jaisor/wifi-climate-sensor/assets/schematic_eagle.sch

## EAGLE design assets/schematic_eagle.sch (2025-02-25)

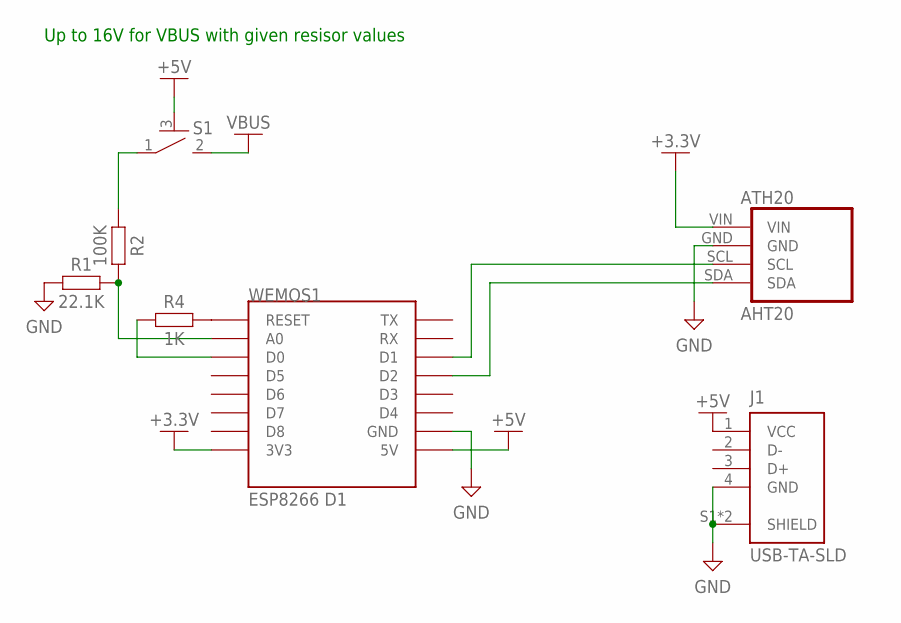
[picture p8: schematic schematic_eagle.sch]

Parts:
ATH20: AHT20
J1: USB-TA-SLD
R1: 22.1K; RESC2012X65
R2: 100K; RESC2012X65
R4: 1K; RESC2012X65
S1: SMD_SWB3U-1100P(M)1100P(M); SMD_SW
WEMOS1: U1; WEMOS-D1-MINI

Connections:
+3.3V: ATH20.VIN, WEMOS1.3V3
+5V: J1.1 (VCC), S1.3, WEMOS1.5V
GND: ATH20.GND, J1.4 (GND), J1.S1 (SHIELD), R1.1, WEMOS1.GND
unnamed: ATH20.SCL, WEMOS1.D1
unnamed: ATH20.SDA, WEMOS1.D2
unnamed: R4.2, WEMOS1.RESET
unnamed: R4.1, WEMOS1.D0
unnamed: R1.2, R2.2, WEMOS1.A0
unnamed: R2.1, S1.1
VBUS: S1.2

Notes on the sheet:
Up to 16V for VBUS with given resisor values
