jaisor/wifi-climate-sensor/src/Device.cpp

#include <Arduino.h>
#include <functional>
#include <ArduinoLog.h>

#include "Device.h"

#include <Wire.h>

// A device ACKs its address when present, which is enough to tell a BME280 from an AHT20
static bool i2cDevicePresent(uint8_t address) {
  Wire.beginTransmission(address);
  return Wire.endTransmission() == 0;
}

// Repeated-start register read, used to tell the BME280 and BME688 apart: both answer on
// 0x76/0x77, so only the chip id register distinguishes them.
static bool i2cReadRegister(uint8_t address, uint8_t reg, uint8_t *value) {
  Wire.beginTransmission(address);
  Wire.write(reg);
  if (Wire.endTransmission(false) != 0) {
    return false;
  }
  if (Wire.requestFrom(address, (uint8_t)1) != 1) {
    return false;
  }
  *value = Wire.read();
  return true;
}

CDevice::CDevice()
:oneWire(NULL), ds18b20(NULL), bme280(NULL), dht(NULL), aht(NULL), bme688(NULL) {

  tMillisUp = millis();
  tMillisTemp = millis();
  sensorReady = false;

#ifdef OLED
  _display = new Adafruit_SSD1306(OLED_SCREEN_WIDTH, OLED_SCREEN_HEIGHT, &Wire, -1);
  if(!_display->begin(SSD1306_SWITCHCAPVCC, OLED_I2C_ID)) {
      Log.errorln("SSD1306 OLED initialiation failed with ID %x", OLED_I2C_ID);
      while (1);
  }
  _display->clearDisplay();
  _display->setTextColor(WHITE);
#endif

  i2cReady = false;
  tempSensorAddress = 0;
  bme68xVariant = 0;
  bme688ReadingReadyAt = 0;
  gas_resistance = 0;
  tLastIAQPersist = millis();
  lastPersistedBaseline = 0;

  // On some targets the DS18B20 data pin doubles as an I2C line, so leave the bus alone when it is selected
  bool i2cPinConflict = false;
  #if defined(TEMP_SENSOR) && defined(I2C_SDA_PIN) && defined(I2C_SCL_PIN)
    i2cPinConflict = configuration.tempSensor == TEMP_SENSOR_DS18B20
      && (TEMP_SENSOR_PIN == I2C_SDA_PIN || TEMP_SENSOR_PIN == I2C_SCL_PIN);
  #endif

  if (!i2cPinConflict) {
    #if defined(I2C_SDA_PIN) && defined(I2C_SCL_PIN)
      i2cReady = Wire.begin(I2C_SDA_PIN, I2C_SCL_PIN);
      if (!i2cReady) {
        Log.errorln(F("I2C Wire initialization failed on pins SDA:%d, SCL:%d"), I2C_SDA_PIN, I2C_SCL_PIN);
      }
    #else
      Wire.begin();
      i2cReady = true;
    #endif
    delay(1000);
  } else {
    Log.noticeln(F("I2C bus not started, DS18B20 shares a pin with it"));
  }

  tLastReading = 0;

  #if defined(TEMP_SENSOR) && defined(TEMP_SENSOR_AUTODETECT)
  // Adopt whatever climate sensor is actually on the bus when nothing is configured yet,
  // or when the configured I2C sensor does not answer (the board was swapped). An explicit
  // DS18B20/DHT22 choice is left alone, since those are not on I2C at all.
  if (i2cReady) {
    tempSensorType detected = detectI2CTempSensor();
    bool configuredIsI2C = configuration.tempSensor == TEMP_SENSOR_BME280
      || configuration.tempSensor == TEMP_SENSOR_AHT20
      || configuration.tempSensor == TEMP_SENSOR_BME688;

    if (detected != TEMP_SENSOR_UNSUPPORTED
      && detected != configuration.tempSensor
      && (configuration.tempSensor == TEMP_SENSOR_UNSUPPORTED || configuredIsI2C)) {
      Log.noticeln(F("Autodetected climate sensor type %u at I2C 0x%x, replacing configured type %u"),
        detected, tempSensorAddress, configuration.tempSensor);
      configuration.tempSensor = detected;
      EEPROM_saveConfig();
    }
  }
  #endif

  #ifdef TEMP_SENSOR
  switch (configuration.tempSensor) {
    case TEMP_SENSOR_DS18B20: {
      pinMode(TEMP_SENSOR_PIN, INPUT_PULLUP);
      oneWire = new OneWire(TEMP_SENSOR_PIN);
      DeviceAddress da;
      ds18b20 = new DS18B20(oneWire);
      ds18b20->setConfig(DS18B20_CRC);
      ds18b20->begin();

      ds18b20->getAddress(da);
      String addr = "";
      for (uint8_t i = 0; i < 8; i++) {
        if (da[i] < 16) {
          addr += String("o");
        }
        addr += String(da[i], HEX);
      }
      Log.noticeln(F("DS18B20 sensor on pin %d at address: %s"), TEMP_SENSOR_PIN, addr.c_str());
      
      ds18b20->setResolution(12);
      ds18b20->requestTemperatures();

      sensorReady = true;
      tMillisTemp = 0;
    } break;
    
    case TEMP_SENSOR_BME280: {
      if (tempSensorAddress == 0) {
        tempSensorAddress = i2cDevicePresent(BME280_I2C_ID_ALT) ? BME280_I2C_ID_ALT : BME280_I2C_ID;
      }
      bme280 = new Adafruit_BME280();
      if (!bme280->begin(tempSensorAddress)) {
        Log.errorln(F("BME280 sensor initialization failed with ID %x"), tempSensorAddress);
        sensorReady = false;
      } else {
        sensorReady = true;
        tMillisTemp = 0;
      }
      minDelayMs = 100;
      Log.noticeln(F("BME280 Initialized"));
    } break;

    case TEMP_SENSOR_DHT22: {
      dht = new DHT_Unified(TEMP_SENSOR_PIN, DHT22);
      dht->begin();
      sensor_t sensor;
      dht->temperature().getSensor(&sensor);
      Log.noticeln(F("DHT temperature sensor name(%s) v(%u) id(%u) range(%F - %F) res(%F)"),
        sensor.name, sensor.version, sensor.sensor_id, 
        sensor.min_value, sensor.max_value, sensor.resolution);
      dht->humidity().getSensor(&sensor);
      Log.noticeln(F("DHT humidity sensor name(%s) v(%u) id(%u) range(%F - %F) res(%F)"),
        sensor.name, sensor.version, sensor.sensor_id, 
        sensor.min_value, sensor.max_value, sensor.resolution);
      minDelayMs = sensor.min_delay / 1000;
      Log.noticeln(F("DHT sensor min delay %i"), minDelayMs);
    } break;

    case TEMP_SENSOR_AHT20: {
      tempSensorAddress = AHT20_I2C_ID;
      aht = new Adafruit_AHTX0();
      if (!aht->begin()) {
        Log.errorln("Failed to initialize AHT sensor, check wiring");
        sensorReady = false;
      } else {
        sensorReady = true;
        tMillisTemp = 0;
      }
      minDelayMs = 100;
      Log.noticeln(F("AHT20 Initialized"));
    } break;

    case TEMP_SENSOR_BME688: {
      if (tempSensorAddress == 0) {
        tempSensorAddress = i2cDevicePresent(BME280_I2C_ID_ALT) ? BME280_I2C_ID_ALT : BME280_I2C_ID;
      }
      bme688 = new Adafruit_BME680(&Wire);
      if (!bme688->begin(tempSensorAddress, true)) {
        Log.errorln(F("BME688 sensor initialization failed with ID %x"), tempSensorAddress);
        sensorReady = false;
      } else {
        bme688->setTemperatureOversampling(BME680_OS_8X);
        bme688->setHumidityOversampling(BME680_OS_2X);
        bme688->setPressureOversampling(BME680_OS_4X);
        bme688->setIIRFilterSize(BME680_FILTER_SIZE_3);
        bme688->setGasHeater(BME688_GAS_HEATER_TEMP_C, BME688_GAS_HEATER_MS);
        sensorReady = true;
        tMillisTemp = 0;
      }
      // The gas heater makes a reading take a few hundred ms, so it is run asynchronously
      // via beginReading()/endReading() rather than blocking the loop.
      minDelayMs = 100;
      bme688ReadingReadyAt = 0;

      // Continue the baseline saved before the last sleep or restart rather than starting
      // over. Time spent asleep is credited so the day-scale decay tracks wall clock time;
      // the configured interval is the only estimate of it available before NTP is up.
      airQuality.restore(configuration.iaqBaseline, configuration.iaqAccumulatedSec);
      lastPersistedBaseline = configuration.iaqBaseline;
      if (configuration.deepSleepDurationSec > 0 && airQuality.hasBaseline()) {
        airQuality.addElapsedSeconds(configuration.deepSleepDurationSec);
      }

      Log.noticeln(F("%s Initialized"),
        bme68xVariant == BME68X_VARIANT_BME688 ? "BME688" : "BME680");
    } break;

    default:
      sensorReady = false;
      Log.errorln(F("Unsupported temperature sensor: %u"), configuration.tempSensor);
      break;
  }
  #endif

  #ifdef CURRENT_SENSOR
  // Skipped when the bus never came up, so the library cannot quietly re-init it on default pins
  ina219 = i2cReady ? new Adafruit_INA219(INA219_I2C_ID) : NULL;
  currentSensorReady = ina219 != NULL && ina219->begin();
  if (currentSensorReady) {
    Log.noticeln(F("INA219 initialized with ID %x"), INA219_I2C_ID);
  } else {
    Log.warningln(F("INA219 not found with ID %x, current sensing disabled"), INA219_I2C_ID);
    delete ina219;
    ina219 = NULL;
  }
  tMillisCurrent = 0;
  tLastCurrentReading = 0;
  loadVoltage = loadCurrent_mA = loadPower_mW = 0;
  #endif

  #ifdef VOLTAGE_SENSOR
      
  #if defined(CONFIG_IDF_TARGET_ESP32C3)
    pinMode(VOLTAGE_SENSOR_ADC_PIN, ANALOG);
    analogSetPinAttenuation(VOLTAGE_SENSOR_ADC_PIN, ADC_11db);
    analogReadResolution(12);
  #elif defined(SEEED_XIAO_M0)
    pinMode(VOLTAGE_SENSOR_ADC_PIN, ANALOG);
    analogReadResolution(12);
  #elif defined(ESP8266)
    pinMode(VOLTAGE_SENSOR_ADC_PIN, INPUT);
  #endif

  #endif

#if defined(ESP32)
#elif defined(ESP8266)
#elif defined(SEEED_XIAO_M0)
#endif
  
  Log.infoln(F("Device initialized"));
}

#if defined(TEMP_SENSOR) && defined(TEMP_SENSOR_AUTODETECT)
// Probes the addresses the two supported I2C climate sensors use and records which one
// answered, so the BME280 can later be opened on whichever of its two addresses is strapped.
tempSensorType CDevice::detectI2CTempSensor() {
  const uint8_t boschAddresses[] = { BME280_I2C_ID, BME280_I2C_ID_ALT };
  for (uint8_t i = 0; i < sizeof(boschAddresses); i++) {
    uint8_t address = boschAddresses[i];
    uint8_t chipId = 0;
    if (!i2cDevicePresent(address) || !i2cReadRegister(address, BOSCH_REG_CHIP_ID, &chipId)) {
      continue;
    }

    switch (chipId) {
      case BOSCH_CHIP_ID_BME280:
        tempSensorAddress = address;
        Log.noticeln(F("Found BME280 at I2C 0x%x"), address);
        return TEMP_SENSOR_BME280;

      case BOSCH_CHIP_ID_BME68X: {
        tempSensorAddress = address;
        // Same chip id for both; the variant register separates the BME688 from the BME680
        bme68xVariant = 0;
        i2cReadRegister(address, BME68X_REG_VARIANT, &bme68xVariant);
        Log.noticeln(F("Found %s at I2C 0x%x"),
          bme68xVariant == BME68X_VARIANT_BME688 ? "BME688" : "BME680", address);
        return TEMP_SENSOR_BME688;
      }

      default:
        // Most likely a BMP280 (0x58), which has no humidity and is not supported here
        Log.warningln(F("Unrecognized Bosch chip id 0x%x at I2C 0x%x, ignoring"), chipId, address);
        break;
    }
  }

  if (i2cDevicePresent(AHT20_I2C_ID)) {
    tempSensorAddress = AHT20_I2C_ID;
    Log.noticeln(F("Found AHT20 at I2C 0x%x"), tempSensorAddress);
    return TEMP_SENSOR_AHT20;
  }

  Log.noticeln(F("No I2C climate sensor found"));
  return TEMP_SENSOR_UNSUPPORTED;
}
#endif

CDevice::~CDevice() { 
  delete ds18b20;
  delete bme280;
  delete dht;
  delete aht;
  delete bme688;
#ifdef CURRENT_SENSOR
  delete ina219;
#endif
#ifdef OLED
  delete _display;
#endif
  Log.noticeln(F("Device destroyed"));
}

void CDevice::loop() {

  #ifdef VOLTAGE_SENSOR
  if (millis() - voltageSensorDelay > 50 || voltageValues.size() < VOLTAGE_SAMPLES) {
    voltageSensorDelay = millis();
    voltageValues.push_back(analogRead(VOLTAGE_SENSOR_ADC_PIN));
    if(voltageValues.size() > VOLTAGE_SAMPLES){
        voltageValues.pop_front();
    }
    voltageAvg = 0;
    for(uint16_t i : voltageValues){
      voltageAvg += i;
    }
    voltageAvg = voltageAvg / voltageValues.size();
  } 
  #endif

  #ifdef CURRENT_SENSOR
  if (ina219 != NULL && millis() - tMillisCurrent > CURRENT_SENSOR_DELAY_MS) {
    tMillisCurrent = millis();
    // Bus voltage is measured on the load side of the shunt, so add the shunt drop back in
    float shunt_mV = ina219->getShuntVoltage_mV();
    float bus_V = ina219->getBusVoltage_V();
    loadVoltage = bus_V + shunt_mV / 1000.0f;
    loadCurrent_mA = ina219->getCurrent_mA();
    loadPower_mW = ina219->getPower_mW();
    tLastCurrentReading = millis();
    Log.traceln(F("INA219 bus: %FV shunt: %FmV load: %FV current: %FmA power: %FmW"),
      bus_V, shunt_mV, loadVoltage, loadCurrent_mA, loadPower_mW);
  }
  #endif

  #ifdef TEMP_SENSOR
  uint32_t delayMs = 1000;
  if (configuration.tempSensor == TEMP_SENSOR_DHT22 || 
    configuration.tempSensor == TEMP_SENSOR_BME280 || 
    configuration.tempSensor == TEMP_SENSOR_AHT20 ||
    configuration.tempSensor == TEMP_SENSOR_BME688) {
    delayMs += minDelayMs;
  }

  if (!sensorReady || millis() - tMillisTemp < delayMs) {
    return;
  } else {
    tMillisTemp = millis();
  }

  switch (configuration.tempSensor) {
    case TEMP_SENSOR_DS18B20: {
      if (ds18b20->isConversionComplete()) {
        temperature = ds18b20->getTempC();
        ds18b20->setResolution(12);
        ds18b20->requestTemperatures();
        tLastReading = millis();
        Log.traceln(F("DS18B20 temp: %FC %FF"), temperature, temperature*1.8+32);
      } else {
        Log.warningln(F("DS18B20 conversion not complete"));
        delay(100);
      }
    } break;
    
    case TEMP_SENSOR_BME280: {
      temperature = bme280->readTemperature();
      humidity = bme280->readHumidity();
      baro_pressure = bme280->readPressure();
      tLastReading = millis();
    } break;

    case TEMP_SENSOR_DHT22: {
      if (millis() - tLastReading > delayMs) {
        sensors_event_t event;
        // temperature
        dht->temperature().getEvent(&event);
        if (isnan(event.temperature)) {
          //Log.warningln(F("Error reading DHT temperature!"));
        } else {
          temperature = event.temperature;
          Log.traceln(F("DHT temp: %FC %FF"), temperature, temperature*1.8+32);
        }
        // humidity
        dht->humidity().getEvent(&event);
        if (isnan(event.relative_humidity)) {
          //Log.warningln(F("Error reading DHT humidity!"));
        }
        else {
          humidity = event.relative_humidity;
          Log.traceln(F("DHT humidity: %F%%"), humidity);
        }
        
        tLastReading = millis();
      }
    } break;

    case TEMP_SENSOR_AHT20: {
      if (millis() - tLastReading > delayMs) {
        sensors_event_t eh, et;
        bool goodRead = aht->getEvent(&eh, &et);
        if (goodRead) {
          // temperature
          if (isnan(et.temperature)) {
            Log.warningln(F("Error reading AHT temperature!"));
            goodRead = false;
          } else {
            temperature = et.temperature;
            Log.traceln("AHT temp: %FC %FF", temperature, temperature*1.8+32);
          }
          // humidity
          if (isnan(eh.relative_humidity)) {
            Log.warningln(F("Error reading AHT humidity!"));
            goodRead = false;
          }
          else {
            humidity = eh.relative_humidity;
            Log.traceln("AHT humidity: %F%%", humidity);
          }
          tLastReading = millis();
        } else {
          Log.warningln(F("Error getting AHT event!"));
          //tLastReading = millis();
        }
      }
    } break;

    case TEMP_SENSOR_BME688: {
      // Forced-mode reading in two steps so the gas heater settling time is not spent blocking
      if (bme688ReadingReadyAt == 0) {
        bme688ReadingReadyAt = bme688->beginReading();
        if (bme688ReadingReadyAt == 0) {
          Log.warningln(F("BME688 failed to start a reading"));
        }
      } else if ((int32_t)(millis() - bme688ReadingReadyAt) >= 0) {
        if (bme688->endReading()) {
          temperature = bme688->temperature;
          humidity = bme688->humidity;
          baro_pressure = bme688->pressure;
          gas_resistance = bme688->gas_resistance;
          airQuality.update(temperature, humidity, gas_resistance);
          persistAirQuality();
          tLastReading = millis();
          Log.traceln(F("BME688 temp: %FC humidity: %F%% pressure: %FPa gas: %FOhm"),
            temperature, humidity, baro_pressure, gas_resistance);
        } else {
          Log.warningln(F("BME688 failed to complete a reading"));
        }
        bme688ReadingReadyAt = 0;
      }
    } break;

    default:
      break;
  }
  #endif

  #if !defined(ESP8266) || (defined(ESP8266) && defined(DISABLE_LOGGING))
  //.sync();
  #endif

  #ifdef OLED
  char st[256];
  
  _display->setTextSize(0);
  _display->setCursor(0,17);
  _display->setTextSize(1);  
  float t = getTemperature(NULL);
  snprintf(st, 256, "Temperature: %0.1f%s\n", configuration.tempUnit == TEMP_UNIT_CELSIUS ? t : t * 1.8 + 32, configuration.tempUnit == TEMP_UNIT_CELSIUS ? "C" : "F");
  _display->print(st);
  snprintf(st, 256, "Humidity: %0.1f%%", getHumidity(NULL));
  _display->print(st);

  #endif

}

#ifdef TEMP_SENSOR
float CDevice::getTemperature(bool *current) {
  if (current != NULL) { 
    *current = millis() - tLastReading < STALE_READING_AGE_MS; 
  }

  return configuration.tempSensor != TEMP_SENSOR_UNSUPPORTED ? temperature: 0;
}

float CDevice::getHumidity(bool *current) {
  if (current != NULL) { 
    *current = millis() - tLastReading < STALE_READING_AGE_MS; 
  }
  return configuration.tempSensor != TEMP_SENSOR_UNSUPPORTED ? humidity: 0;
}

float CDevice::getBaroPressure(bool *current) {
  if (current != NULL) { 
    *current = millis() - tLastReading < STALE_READING_AGE_MS; 
  }
  return configuration.tempSensor == TEMP_SENSOR_BME280
    || configuration.tempSensor == TEMP_SENSOR_BME688 ? baro_pressure: 0;
}

float CDevice::getGasResistance(bool *current) {
  if (current != NULL) { 
    *current = configuration.tempSensor == TEMP_SENSOR_BME688
      && millis() - tLastReading < STALE_READING_AGE_MS; 
  }
  return configuration.tempSensor == TEMP_SENSOR_BME688 ? gas_resistance: 0;
}

float CDevice::getIAQ(bool *current) {
  if (current != NULL) {
    *current = configuration.tempSensor == TEMP_SENSOR_BME688
      && airQuality.isValid()
      && millis() - tLastReading < STALE_READING_AGE_MS;
  }
  return airQuality.getIAQ();
}

uint8_t CDevice::getIAQAccuracy() {
  return configuration.tempSensor == TEMP_SENSOR_BME688 ? airQuality.getAccuracy() : 0;
}

const char* CDevice::getIAQRating() {
  return configuration.tempSensor == TEMP_SENSOR_BME688 ? airQuality.getRating() : "";
}

const char* CDevice::getIAQAccuracyText() {
  return configuration.tempSensor == TEMP_SENSOR_BME688 ? airQuality.getAccuracyText() : "";
}

void CDevice::persistAirQuality(bool force) {
  if (configuration.tempSensor != TEMP_SENSOR_BME688 || !airQuality.hasBaseline()) {
    return;
  }

  float baseline = airQuality.getBaseline();

  if (!force) {
    // Flash wear: the baseline moves slowly, so saving on every reading would be pointless
    // as well as damaging. Only write on a real change, and never more often than the interval.
    if (millis() - tLastIAQPersist < IAQ_PERSIST_INTERVAL_MS) {
      return;
    }
    if (lastPersistedBaseline > 0
      && fabsf(baseline - lastPersistedBaseline) < lastPersistedBaseline * IAQ_PERSIST_DELTA) {
      tLastIAQPersist = millis();
      return;
    }
  }

  configuration.iaqMagic = IAQ_STATE_MAGIC;
  configuration.iaqBaseline = baseline;
  configuration.iaqAccumulatedSec = airQuality.getAccumulatedSeconds();
  EEPROM_saveConfig();

  tLastIAQPersist = millis();
  lastPersistedBaseline = baseline;
  Log.infoln(F("Persisted IAQ baseline %F Ohm at %u tracked seconds"),
    baseline, configuration.iaqAccumulatedSec);
}

const char* CDevice::getTempSensorName() {
  switch (configuration.tempSensor) {
    case TEMP_SENSOR_DS18B20: return "DS18B20";
    case TEMP_SENSOR_BME280:  return "BME280";
    case TEMP_SENSOR_DHT22:   return "DHT22";
    case TEMP_SENSOR_AHT20:   return "AHT20";
    case TEMP_SENSOR_BME688:  return bme68xVariant == BME68X_VARIANT_BME688 ? "BME688" : "BME680";
    default:                  return "none";
  }
}
#endif


#ifdef VOLTAGE_SENSOR
float CDevice::getVoltage(bool *current) {
  if (current != NULL) { *current = true; }
  float v = voltageAvg / configuration.voltageDivider;
  Log.verboseln(F("Voltage avg raw: %u volts: %F over %u samples"), voltageAvg, v, voltageValues.size());
  return v;
}
uint16_t CDevice::getVoltageADC(bool *current) {
  if (current != NULL) { *current = true; }
  return voltageAvg;
}
#endif

#ifdef CURRENT_SENSOR
float CDevice::getLoadVoltage(bool *current) {
  if (current != NULL) {
    *current = currentSensorReady && millis() - tLastCurrentReading < STALE_READING_AGE_MS;
  }
  return loadVoltage;
}

float CDevice::getLoadCurrent(bool *current) {
  if (current != NULL) {
    *current = currentSensorReady && millis() - tLastCurrentReading < STALE_READING_AGE_MS;
  }
  return loadCurrent_mA;
}

float CDevice::getLoadPower(bool *current) {
  if (current != NULL) {
    *current = currentSensorReady && millis() - tLastCurrentReading < STALE_READING_AGE_MS;
  }
  return loadPower_mW;
}
#endif

JsonDocument& CDevice::getDeviceSettings() {

  jsonDeviceSettings["name"] = configuration.name;
  jsonDeviceSettings["wifiSsid"] = configuration.wifiSsid;

  #ifdef TEMP_SENSOR
  jsonDeviceSettings["tempSensor"] = configuration.tempSensor;
  
  switch (configuration.tempSensor) {
    case TEMP_SENSOR_DS18B20: jsonDeviceSettings["tempSensorStr"] = "DS18B20"; break;
    case TEMP_SENSOR_BME280: jsonDeviceSettings["tempSensorStr"] = "BME280"; break;
    case TEMP_SENSOR_DHT22: jsonDeviceSettings["tempSensorStr"] = "DHT22"; break;
    case TEMP_SENSOR_AHT20: jsonDeviceSettings["tempSensorStr"] = "AHT20"; break;
    case TEMP_SENSOR_BME688: jsonDeviceSettings["tempSensorStr"] = getTempSensorName(); break;
    default: jsonDeviceSettings["tempSensorStr"] = "`"; break;
  }

  jsonDeviceSettings["tCorrection"][0]["actual"] = configuration.tCorrection[0].actual;
  jsonDeviceSettings["tCorrection"][0]["measured"] = configuration.tCorrection[0].measured;
  jsonDeviceSettings["tCorrection"][1]["actual"] = configuration.tCorrection[1].actual;
  jsonDeviceSettings["tCorrection"][1]["measured"] = configuration.tCorrection[1].measured;

  jsonDeviceSettings["hCorrection"][0]["actual"] = configuration.hCorrection[0].actual;
  jsonDeviceSettings["hCorrection"][0]["measured"] = configuration.hCorrection[0].measured;
  jsonDeviceSettings["hCorrection"][1]["actual"] = configuration.hCorrection[1].actual;
  jsonDeviceSettings["hCorrection"][1]["measured"] = configuration.hCorrection[1].measured;

  jsonDeviceSettings["tempUnit"] = configuration.tempUnit;
  jsonDeviceSettings["tempSensorAddress"] = tempSensorAddress;
  #endif

  #ifdef CURRENT_SENSOR
  jsonDeviceSettings["currentSensorReady"] = currentSensorReady;
  jsonDeviceSettings["currentSensorStr"] = currentSensorReady ? "INA219" : "-";
  #endif

  jsonDeviceSettings["ledEnabled"] = configuration.ledEnabled;

  jsonDeviceSettings["deepSleepDurationSec"] = configuration.deepSleepDurationSec;
  #ifdef VOLTAGE_SENSOR
  jsonDeviceSettings["voltageDivider"] = configuration.voltageDivider;
  #endif


  return jsonDeviceSettings;
}

bool CDevice::setDeviceSettings(JsonDocument ac) {
  #ifdef DEBUG_MOCK_HP
    jsonDeviceSettings["temperature"] = ac["temperature"];
    return true;
  #else
    jsonDeviceSettings["temperature"] = ac["temperature"];
    return true;
  #endif
}
