jaisor/wifi-climate-sensor/src/wifi/HTMLAssets.h

#pragma once

#include <Arduino.h>

extern const char htmlTop[];
extern const char htmlBottom[];
extern const char htmlWifi[];
extern const char htmlSensor[];
extern const char htmlDevice[];
extern const char htmlMain[];
extern const char htmlMainPressure[];
extern const char htmlMainGasTop[];
extern const char htmlMainGasBottom[];
extern const char htmlMainGas[];
extern const char htmlMainPower[];

extern const char cssPico[];
