jaisor/wifi-climate-sensor/src/wifi/WifiManager.h

#pragma once

#if defined(ESP32)
  #include <WiFi.h>
  #include <AsyncTCP.h>
#elif defined(ESP8266)
  #include <ESP8266WiFi.h>
  #include <ESPAsyncTCP.h>
#endif
#include <ESPAsyncWebServer.h>
#include <PubSubClient.h>
#include <ArduinoJson.h>
#include <Print.h>

#include "BaseManager.h"
#include "wifi/SensorProvider.h"

#ifdef OLED
  #include <Adafruit_SSD1306.h>
  #include <Adafruit_GFX.h>
#endif

typedef enum {
  WF_CONNECTING = 0,
  WF_LISTENING = 1
} wifi_status;

class CWifiManager: public CBaseManager {

private:
  ISensorProvider *sensorProvider;
  bool postedSensorUpdate;
  bool rebootNeeded;
  uint8_t wifiRetries;
  unsigned long tMillis;
  wifi_status status;
  char softAP_SSID[32];
  char SSID[32];
  char mqttSubcribeTopicConfig[255];
  unsigned long tsAPReboot;
  
  AsyncWebServer* server;
  PubSubClient mqtt;

  JsonDocument sensorJson;
  JsonDocument configJson;

  String currentIP();
  void connect();
  void listen();

  void handleRoot(AsyncWebServerRequest *request);
  void handleWifi(AsyncWebServerRequest *request);
  void handleSensor(AsyncWebServerRequest *request);
  void handleDevice(AsyncWebServerRequest *request);
  void handleFactoryReset(AsyncWebServerRequest *request);
  void handleReboot(AsyncWebServerRequest *request);
  void handleFixMQTT(AsyncWebServerRequest *request);
  void handleStyleCSS(AsyncWebServerRequest *request);
  //
  void handleRestAPI_HP(AsyncWebServerRequest *request);
  void handleRestAPI_Device(AsyncWebServerRequest *request);

  void printHTMLTop(Print *p);
  void printHTMLBottom(Print *p);
  void printHTMLMain(Print *p);
#ifdef TEMP_SENSOR
  void printHTMLIAQHistory(Print *p);
#endif
  void printEnvSensorLabel(char *buf, size_t len);
  void printPowerSensorLabel(char *buf, size_t len);

  bool postSensorUpdate();
  bool isApMode();

  bool updateConfigFromJson(JsonDocument jsonObj);
  bool updateSensorJson();

  void mqttCallback(char *topic, uint8_t *payload, unsigned int);
  void publishHADiscovery();
  void performOTAUpdate(const String& url);
  bool ensureMQTTConnected();

#ifdef OLED
  Adafruit_SSD1306 *display;
#endif

public:
	CWifiManager(ISensorProvider *sensorProvider);
  virtual void loop();

  virtual const bool isRebootNeeded() { return rebootNeeded; }
  virtual const bool isJobDone() { return !isApMode() && postedSensorUpdate; }

#ifdef OLED
  void setDisplay(Adafruit_SSD1306* display) { this->display = display; };
#endif
};
